zhukovin/pitoshi/audio/Model-B-Plus-Audio-Video-Jack-Diagram.png

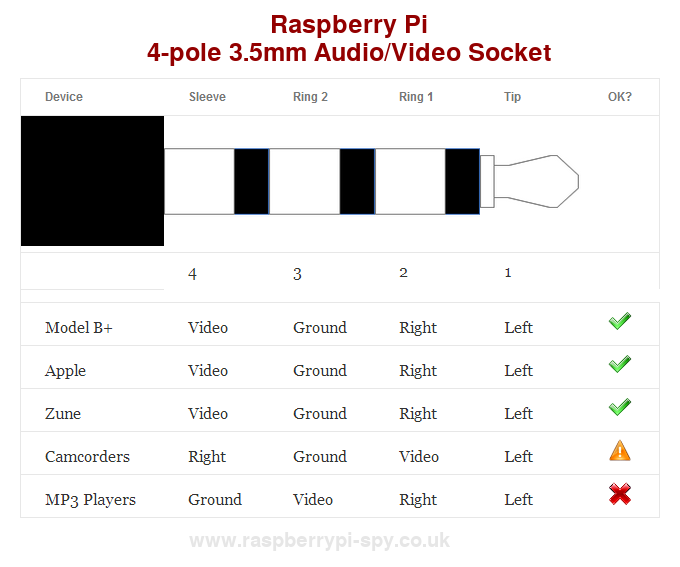
audio/Model-B-Plus-Audio-Video-Jack-Diagram.png
